jonaschramm/race-tracker/v2-simple/kicad/RaceTracker_v2.kicad_sch

## KiCad design v2-simple/kicad/RaceTracker_v2.kicad_sch (2026-08-14)

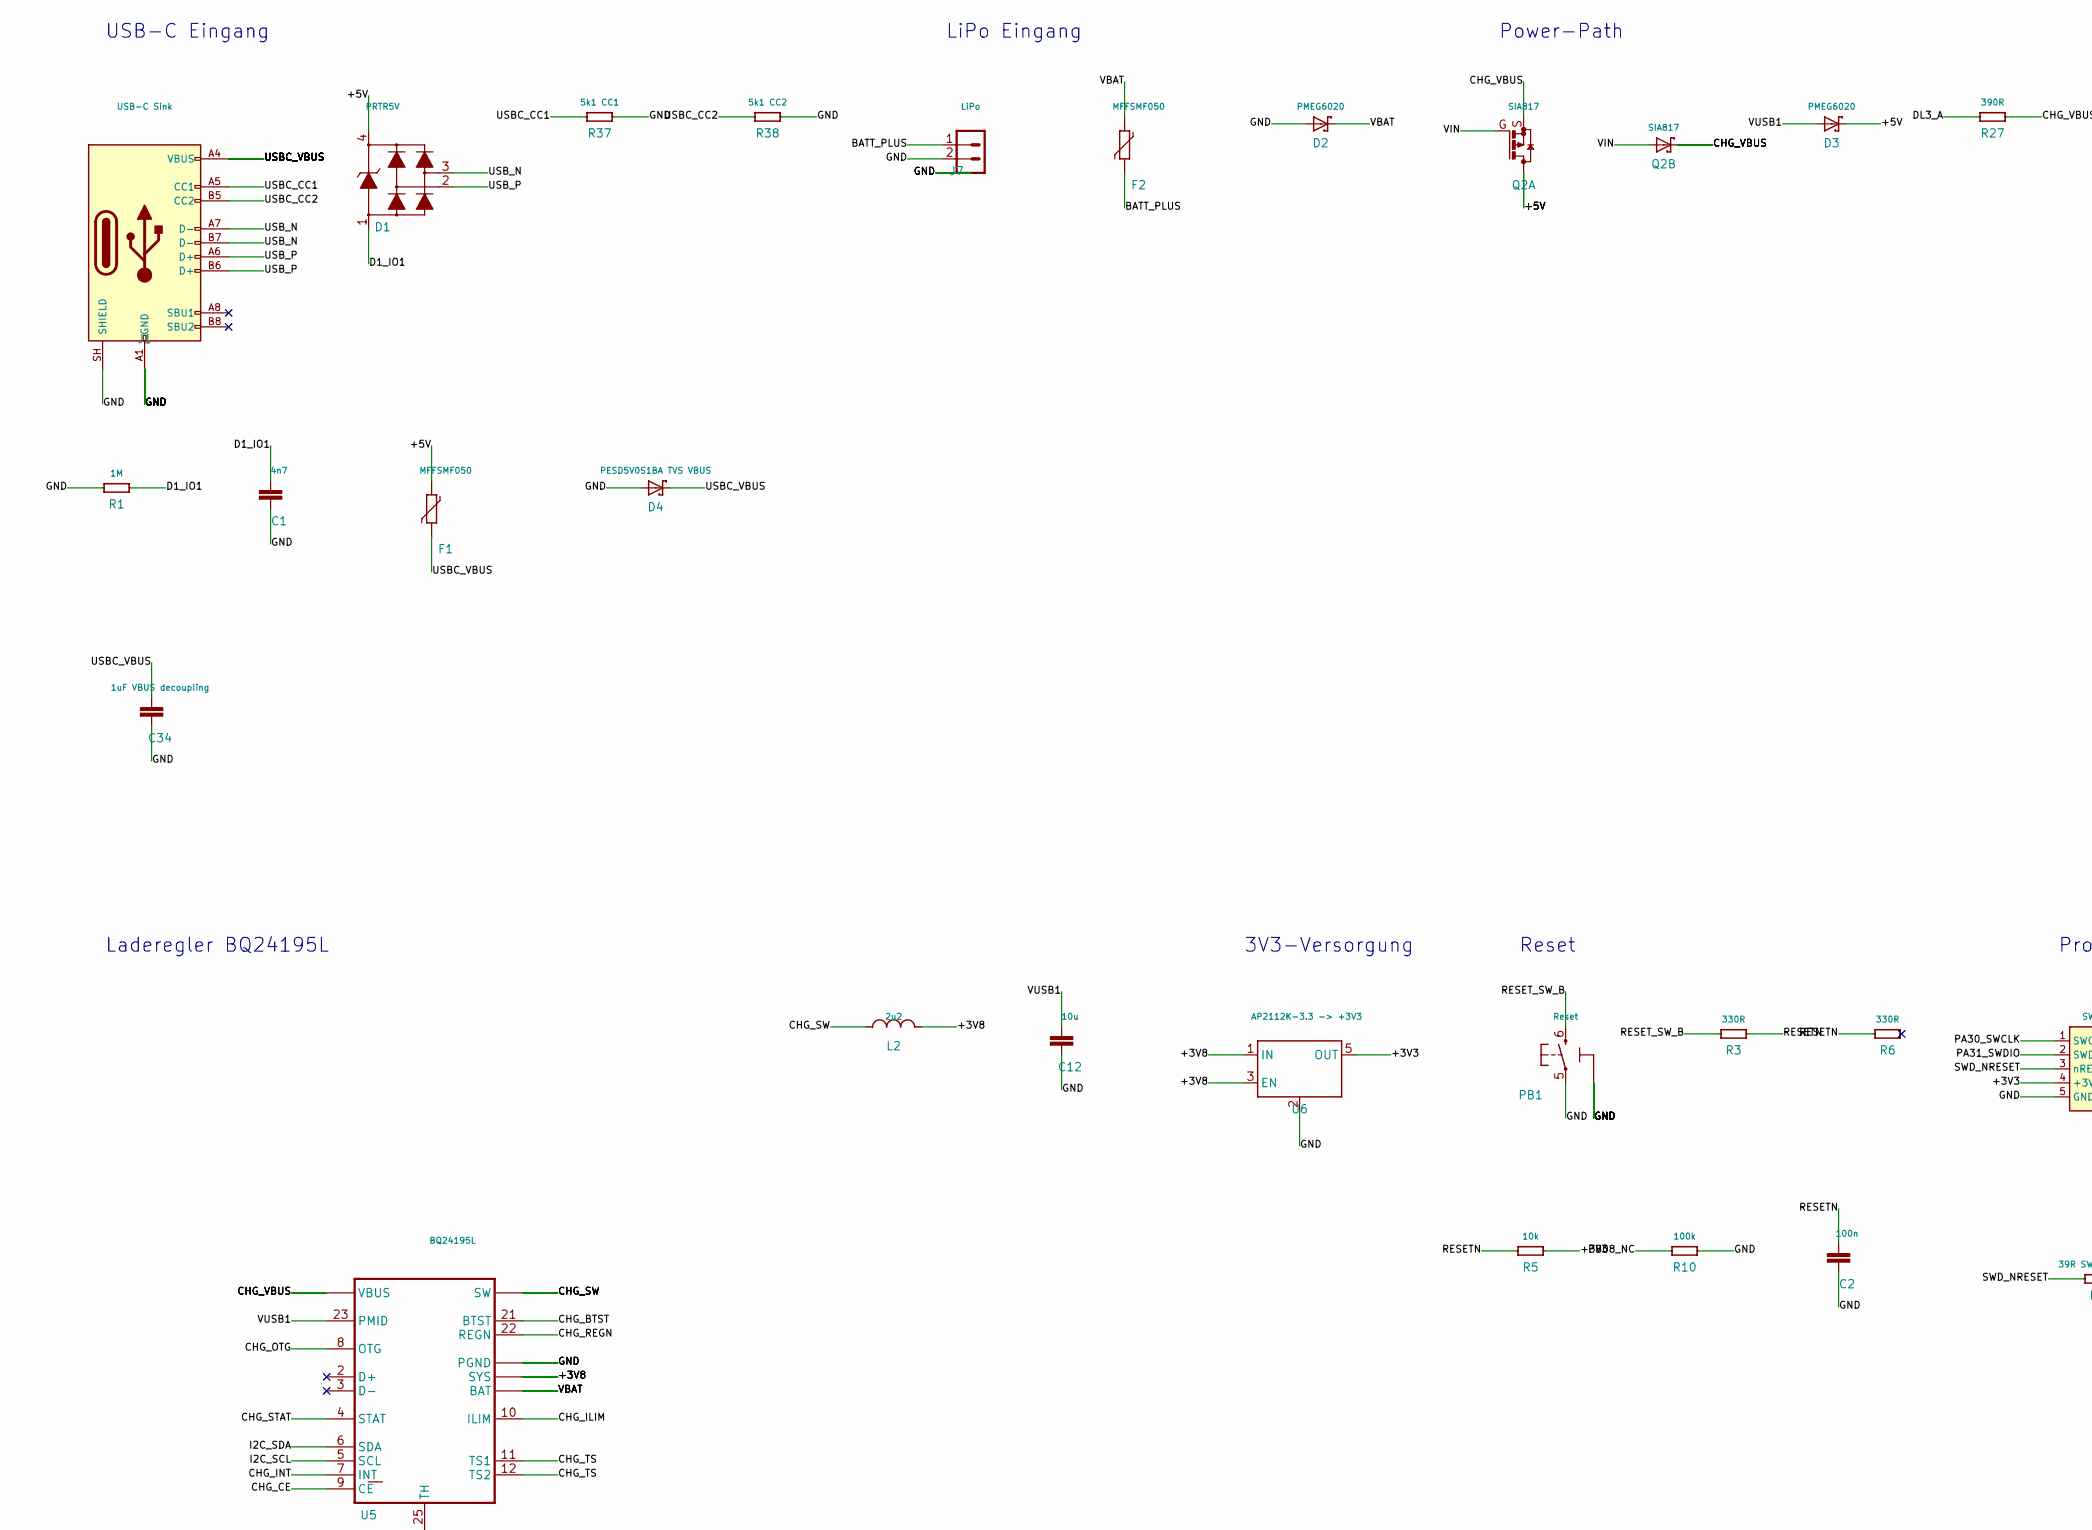
[picture p19: schematic RaceTracker_v2.kicad_sch, part in row 1, column 1]

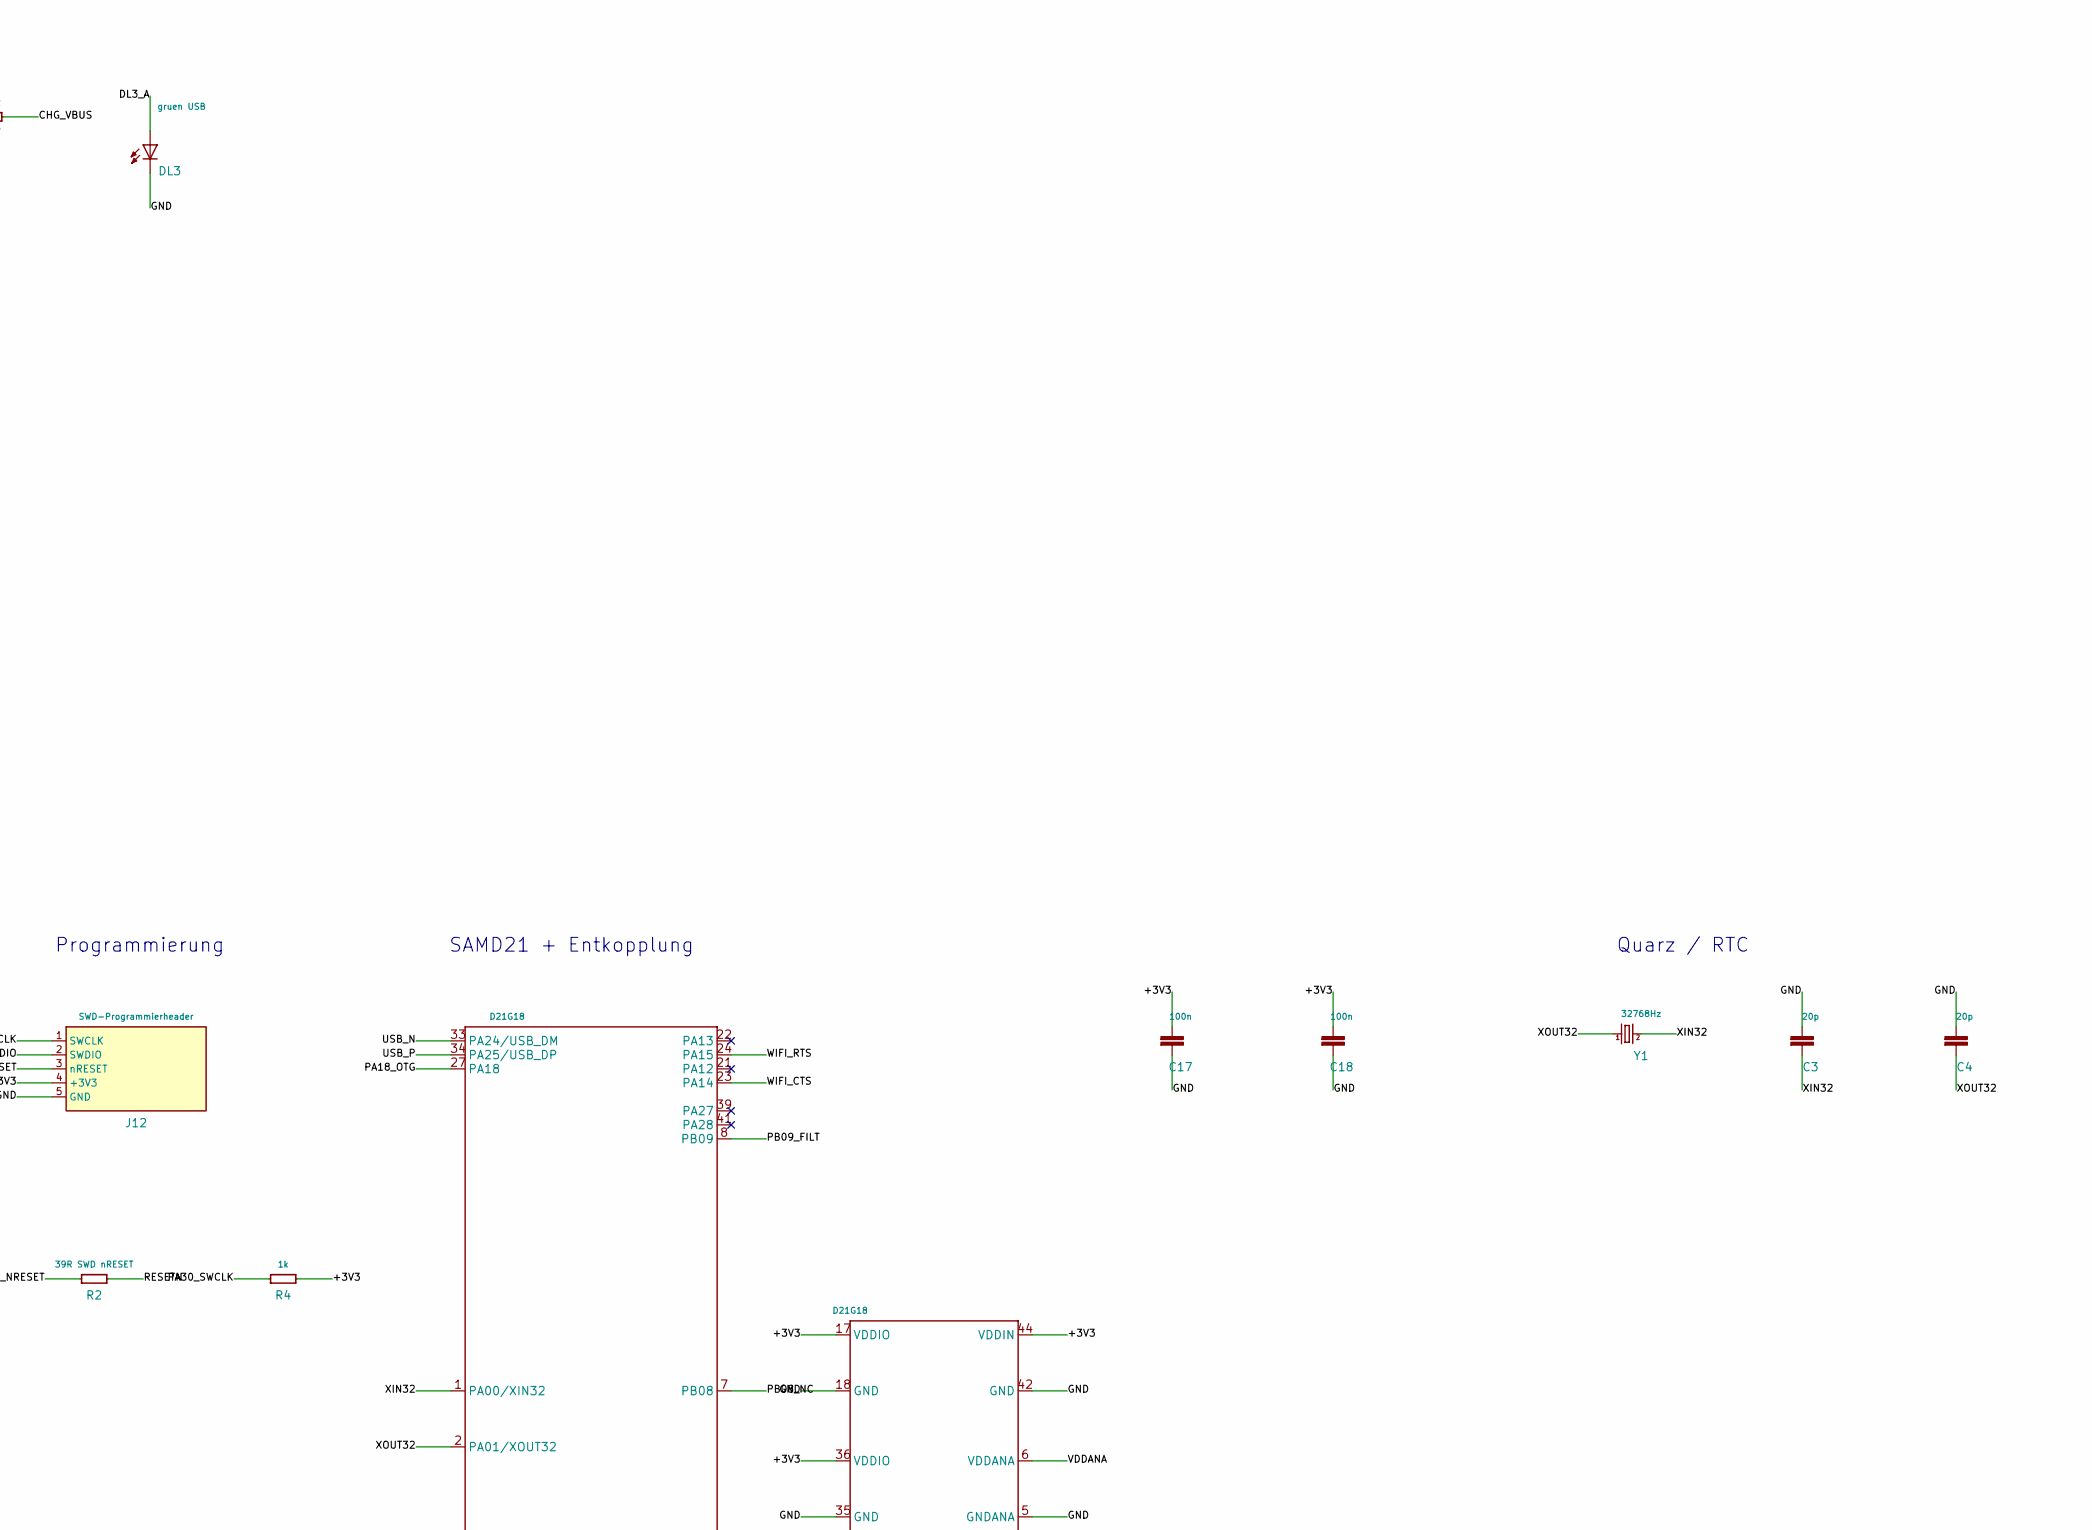
[picture p20: schematic RaceTracker_v2.kicad_sch, part in row 1, column 2]

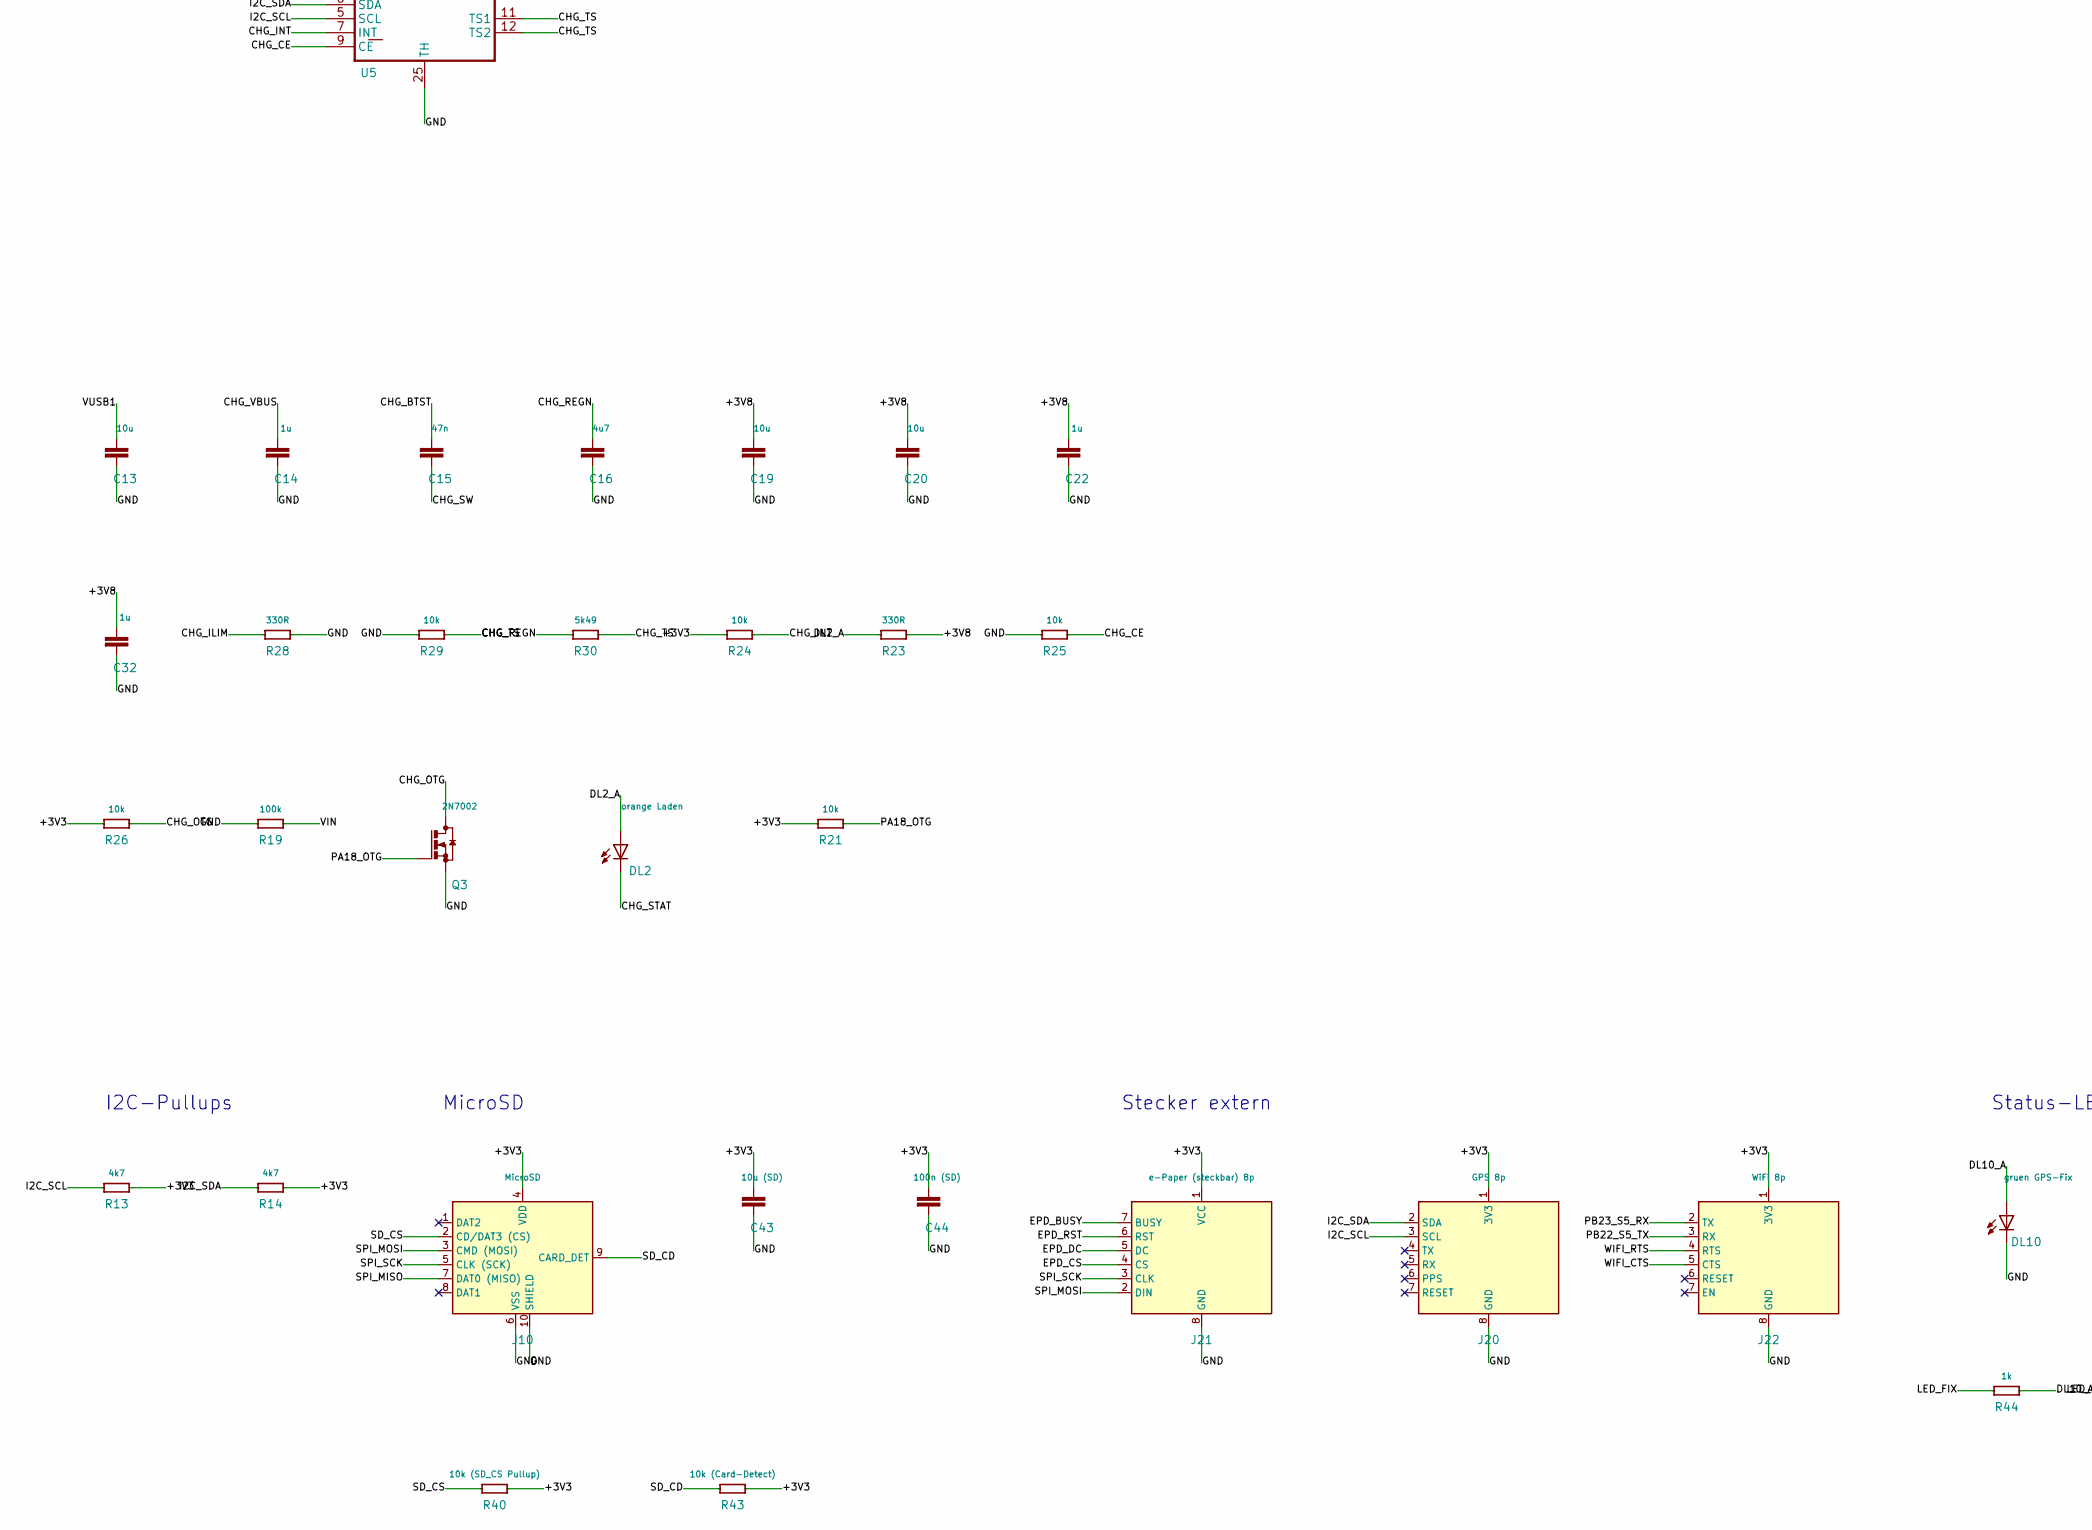
[picture p21: schematic RaceTracker_v2.kicad_sch, part in row 2, column 1]

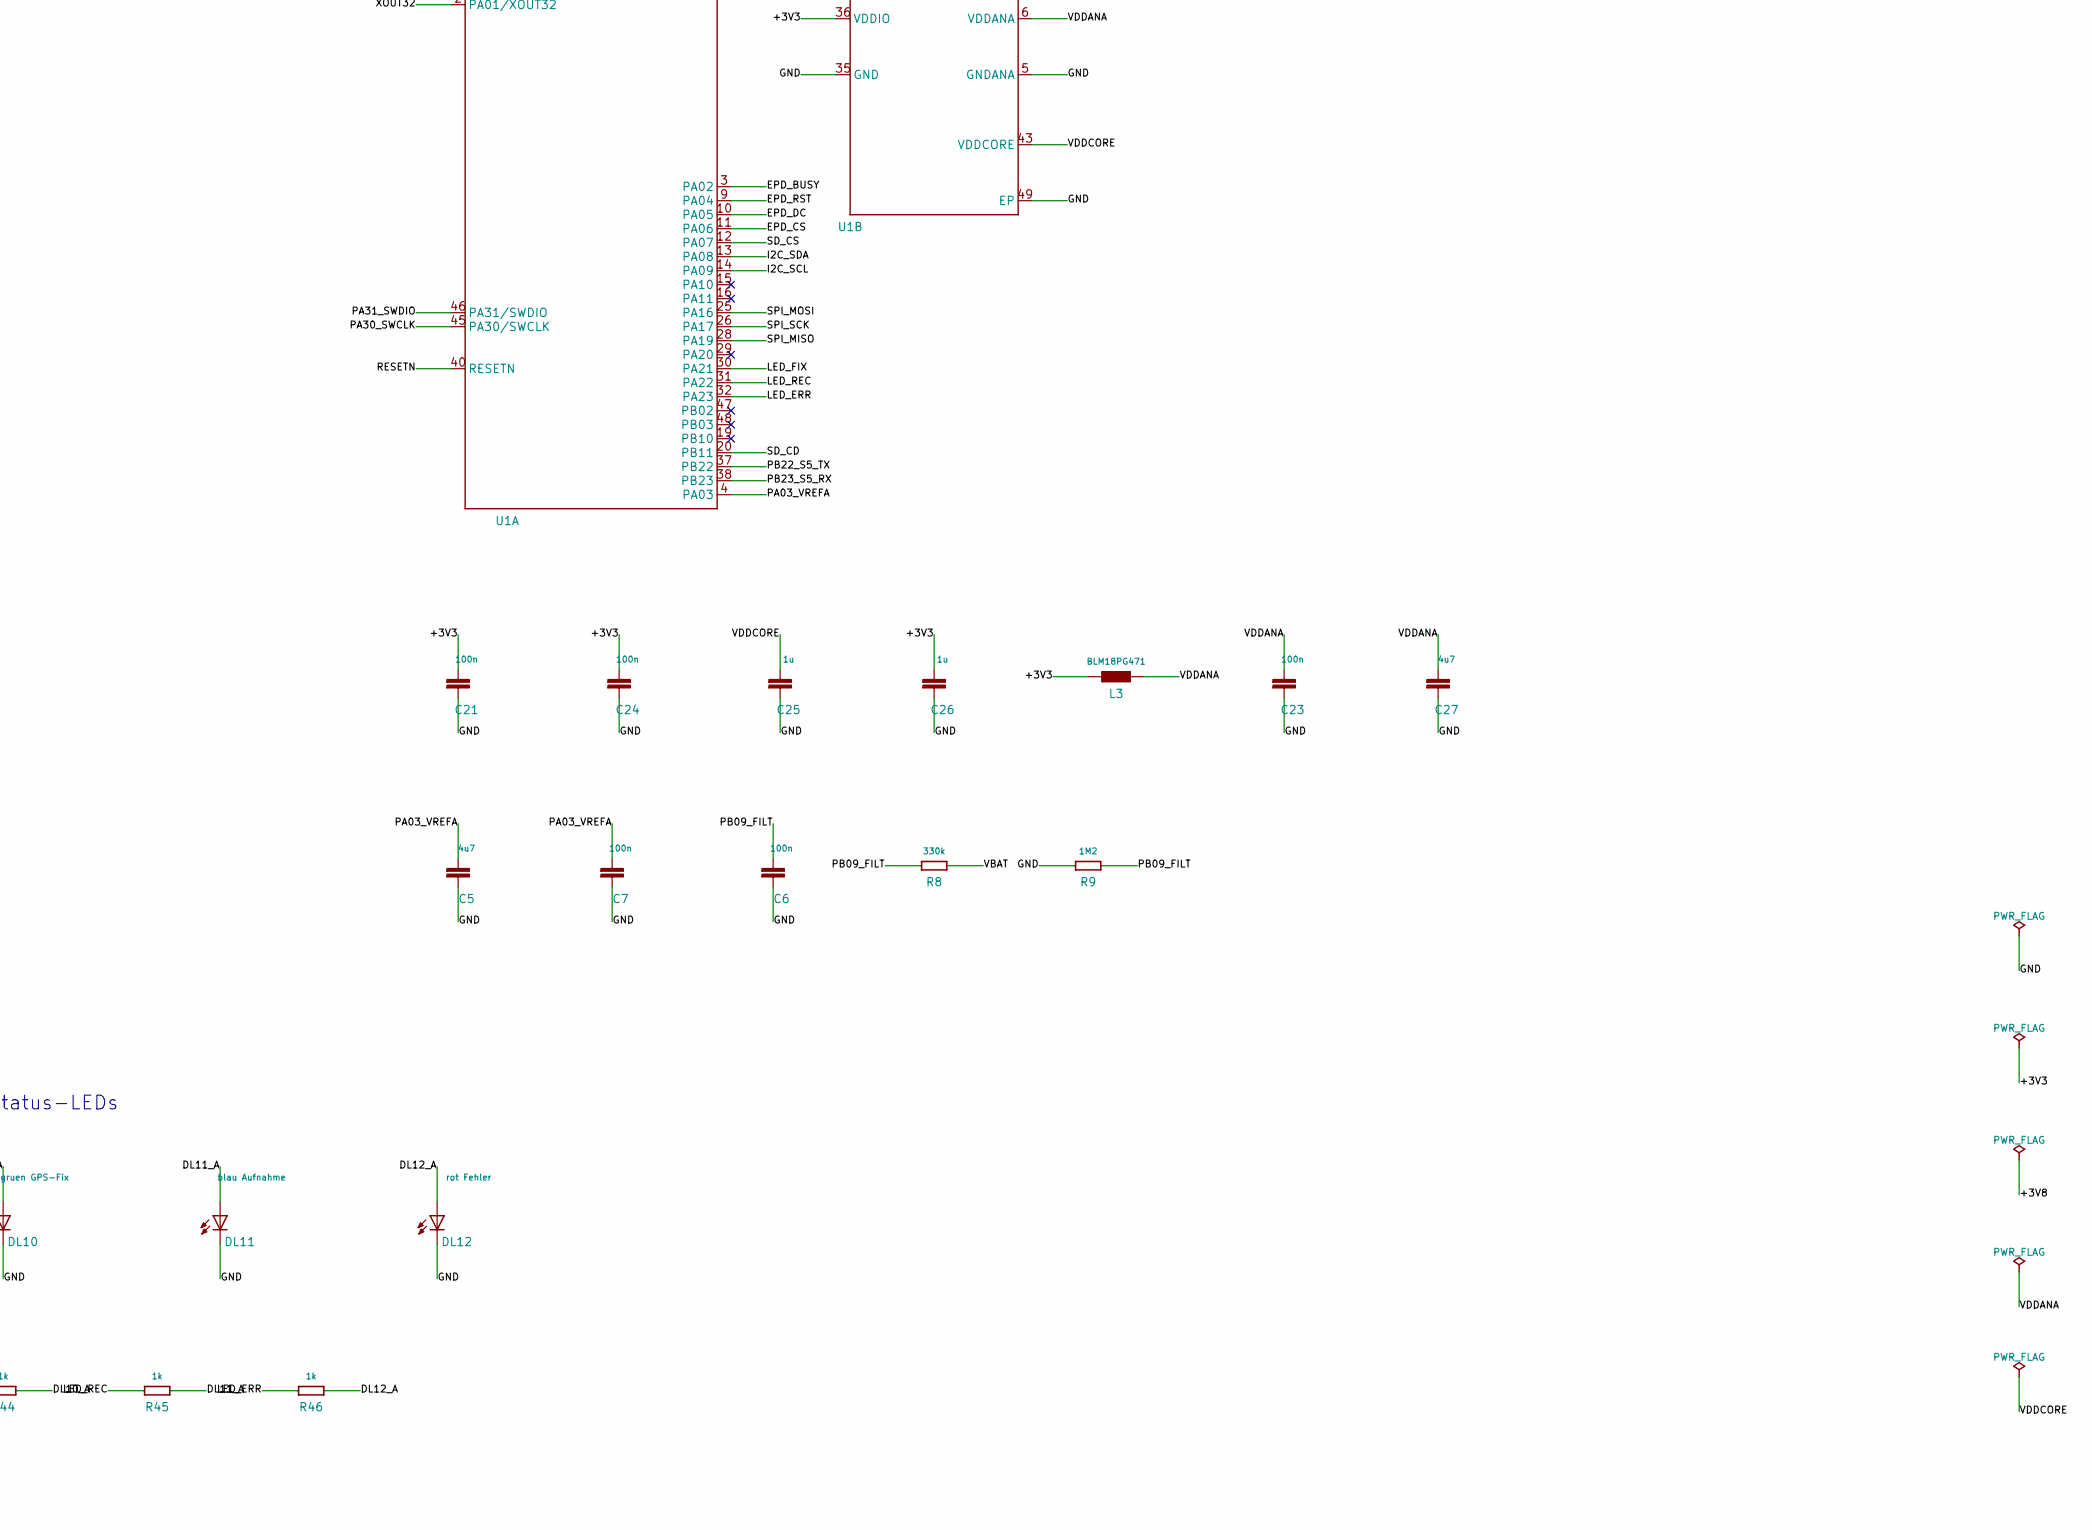
[picture p22: schematic RaceTracker_v2.kicad_sch, part in row 2, column 2]

Parts:
C1: 4n7; C_0805_2012Metric
C2, C6, C7, C17, C18, C21, C23, C24: 100n; C_0402_1005Metric
C3, C4: 20p; C_0402_1005Metric
C5, C16: 4u7; C_0402_1005Metric
C12, C13, C19, C20: 10u; C_0603_1608Metric
C14, C22, C25, C26, C32: 1u; C_0402_1005Metric
C15: 47n; C_0402_1005Metric
C27: 4u7; C_0603_1608Metric
C34: 1uF VBUS decoupling; C_0402_1005Metric
C43: 10u (SD); C_0603_1608Metric
C44: 100n (SD); C_0402_1005Metric
D1: PRTR5V; SOT143B_4N
D2, D3: PMEG6020; SODFL3517X110N
D4: PESD5V0S1BA TVS VBUS; D_SOD-323
DL2: orange Laden; LED_0603_AK
DL3: gruen USB; LED_0603_AK
DL10: gruen GPS-Fix; LED_0603_AK
DL11: blau Aufnahme; LED_0603_AK
DL12: rot Fehler; LED_0603_AK
F1, F2: MFFSMF050; Fuse_0603_1608Metric
J1: USB-C Sink; USB_C_Receptacle_HRO_TYPE-C-31-M-12
J7: LiPo; JST_S2B_PH_SM4_TB
J10: MicroSD; microSD_HC_Molex_104031-0811
J12: SWD-Programmierheader; PinHeader_1x05_P2.54mm_Vertical
J20: GPS 8p; PinHeader_1x08_P2.54mm_Vertical
J21: e-Paper (steckbar) 8p; PinHeader_1x08_P2.54mm_Vertical
J22: WiFi 8p; PinHeader_1x08_P2.54mm_Vertical
L2: 2u2; SRP4020
L3: BLM18PG471; L_0603_1608Metric
PB1: Reset; PTS820_NO_HOLES
Q2: SIA817; SON65P205X205X75-8N-MWSD
Q3: 2N7002; SOTFL50P160X78-3
R1: 1M; R_0402_1005Metric
R2: 39R SWD nRESET; R_0402_1005Metric
R3, R6, R23, R28: 330R; R_0402_1005Metric
R4, R44, R45, R46: 1k; R_0402_1005Metric
R5, R21, R24, R25, R26, R29: 10k; R_0402_1005Metric
R8: 330k; R_0402_1005Metric
R9: 1M2; R_0402_1005Metric
R10, R19: 100k; R_0402_1005Metric
R13, R14: 4k7; R_0402_1005Metric
R27: 390R; R_0402_1005Metric
R30: 5k49; R_0402_1005Metric
R37: 5k1 CC1; R_0402_1005Metric
R38: 5k1 CC2; R_0402_1005Metric
R40: 10k (SD_CS Pullup); R_0402_1005Metric
R43: 10k (Card-Detect); R_0402_1005Metric
U1: D21G18; QFN48_SAMD21G18A
U5: BQ24195L; QFN24_BQ24195L
U6: AP2112K-3.3 -> +3V3; SOT25
Y1: 32768Hz; ABS07_CRYSTAL

Connections:
+3V3: C17.1, C18.1, C21.1, C24.1, C26.1, C43.1, C44.1, J10.4 (VDD), J12.4 (+3V3), J20.1 (3V3), J21.1 (VCC), J22.1 (3V3), L3.1, R4.2, R5.2, R13.2, R14.2, R21.1, R24.1, R26.1, R40.2, R43.2, U1.17 (VDDIO), U1.36 (VDDIO), U1.44 (VDDIN), U6.5 (OUT)
+3V8: C19.1, C20.1, C22.1, C32.1, L2.2, R23.2, U5.15 (SYS), U5.16 (SYS), U6.1 (IN), U6.3 (EN)
+5V: D1.4, D3.C, F1.2, Q2.D, Q2.D2 (D)
BATT_PLUS: F2.1, J7.1
CHG_BTST: C15.1, U5.21 (BTST)
CHG_CE: R25.2, U5.9 (CE)
CHG_ILIM: R28.1, U5.10 (ILIM)
CHG_INT: R24.2, U5.7 (INT)
CHG_OTG: Q3.D, R26.2, U5.8 (OTG)
CHG_REGN: C16.1, R30.1, U5.22 (REGN)
CHG_STAT: DL2.C, U5.4 (STAT)
CHG_SW: C15.2, L2.1, U5.19 (SW), U5.20 (SW)
CHG_TS: R29.2, R30.2, U5.11 (TS1), U5.12 (TS2)
CHG_VBUS: C14.1, Q2.K (C), Q2.K2 (C), Q2.S, R27.2, U5.1 (VBUS), U5.24 (VBUS)
D1_IO1: C1.1, D1.1, R1.2
DL2_A: DL2.A, R23.1
DL3_A: DL3.A, R27.1
DL10_A: DL10.A, R44.2
DL11_A: DL11.A, R45.2
DL12_A: DL12.A, R46.2
EPD_BUSY: J21.7 (BUSY), U1.3 (PA02)
EPD_CS: J21.4 (CS), U1.11 (PA06)
EPD_DC: J21.5 (DC), U1.10 (PA05)
EPD_RST: J21.6 (RST), U1.9 (PA04)
GND: C1.2, C2.2, C3.1, C4.1, C5.2, C6.2, C7.2, C12.2, C13.2, C14.2, C16.2, C17.2, C18.2, C19.2, C20.2, C21.2, C22.2, C23.2, C24.2, C25.2, C26.2, C27.2, C32.2, C34.2, C43.2, C44.2, D2.A, D4.A, DL3.C, DL10.C, DL11.C, DL12.C, J1.A1 (GND), J1.A12 (GND), J1.B1 (GND), J1.B12 (GND), J1.SH (SHIELD), J7.2, J7.3 (SH), J7.4 (SH), J10.6 (VSS), J10.10 (SHIELD), J12.5 (GND), J20.8 (GND), J21.8 (GND), J22.8 (GND), PB1.1 (3), PB1.2 (3), PB1.3, PB1.4 (3), PB1.5 (1), Q3.S, R1.1, R9.1, R10.2, R19.1, R25.1, R28.2, R29.1, R37.2, R38.2, U1.5 (GNDANA), U1.18 (GND), U1.35 (GND), U1.42 (GND), U1.49 (EP), U5.17 (PGND), U5.18 (PGND), U5.25 (TH), U6.2 (GND/ADJ)
I2C_SCL: J20.3 (SCL), R13.1, U1.14 (PA09), U5.5 (SCL)
I2C_SDA: J20.2 (SDA), R14.1, U1.13 (PA08), U5.6 (SDA)
LED_ERR: R46.1, U1.32 (PA23)
LED_FIX: R44.1, U1.30 (PA21)
LED_REC: R45.1, U1.31 (PA22)
PA03_VREFA: C5.1, C7.1, U1.4 (PA03)
PA18_OTG: Q3.G, R21.2, U1.27 (PA18)
PA30_SWCLK: J12.1 (SWCLK), R4.1, U1.45 (PA30/SWCLK)
PA31_SWDIO: J12.2 (SWDIO), U1.46 (PA31/SWDIO)
PB08_NC: R10.1, U1.7 (PB08)
PB09_FILT: C6.1, R8.1, R9.2, U1.8 (PB09)
PB22_S5_TX: J22.3 (RX), U1.37 (PB22)
PB23_S5_RX: J22.2 (TX), U1.38 (PB23)
RESETN: C2.1, R2.2, R3.2, R5.1, R6.1, U1.40 (RESETN)
RESET_SW_B: PB1.6 (2), R3.1
SD_CD: J10.9 (CARD_DET), R43.1, U1.20 (PB11)
SD_CS: J10.2 (CD/DAT3 (CS)), R40.1, U1.12 (PA07)
SPI_MISO: J10.7 (DAT0 (MISO)), U1.28 (PA19)
SPI_MOSI: J10.3 (CMD (MOSI)), J21.2 (DIN), U1.25 (PA16)
SPI_SCK: J10.5 (CLK (SCK)), J21.3 (CLK), U1.26 (PA17)
SWD_NRESET: J12.3 (nRESET), R2.1
USBC_CC1: J1.A5 (CC1), R37.1
USBC_CC2: J1.B5 (CC2), R38.1
USBC_VBUS: C34.1, D4.C, F1.1, J1.A4 (VBUS), J1.A9 (VBUS), J1.B4 (VBUS), J1.B9 (VBUS)
USB_N: D1.3, J1.A7 (D-), J1.B7 (D-), U1.33 (PA24/USB_DM)
USB_P: D1.2, J1.A6 (D+), J1.B6 (D+), U1.34 (PA25/USB_DP)
VBAT: D2.C, F2.2, R8.2, U5.13 (BAT), U5.14 (BAT)
VDDANA: C23.1, C27.1, L3.2, U1.6 (VDDANA)
VDDCORE: C25.1, U1.43 (VDDCORE)
VIN: Q2.A, Q2.G, R19.2
VUSB1: C12.1, C13.1, D3.A, U5.23 (PMID)
WIFI_CTS: J22.5 (CTS), U1.23 (PA14)
WIFI_RTS: J22.4 (RTS), U1.24 (PA15)
XIN32: C3.2, U1.1 (PA00/XIN32), Y1.2
XOUT32: C4.2, U1.2 (PA01/XOUT32), Y1.1

Notes on the sheet:
USB-C Eingang
LiPo Eingang
Power-Path
Laderegler BQ24195L
3V3-Versorgung
SAMD21 + Entkopplung
Quarz / RTC
Reset
I2C-Pullups
Programmierung
MicroSD
Status-LEDs
Stecker extern
