jonaschramm/race-tracker/RaceTracker.kicad_prj/V3 ESP32/tools/pdn_check.py

"""3V3-rail PDN impedance check against the ESP32-S3-WROOM-1's own datasheet
TX current spec, run as a real ngspice AC sweep (not just three spot points).

Datasheet facts used (ESP32-S3-WROOM-1 & WROOM-1U Datasheet v1.8):
  - Table 6-4: worst-case TX peak current = 355 mA (802.11b, 1 Mbps, @20.5 dBm),
    measured "with a 3.3 V supply" -- i.e. directly on VDD33/+3V3, no LDO
    conversion needed in the current number itself.
  - Table 6-2: VDD33 recommended operating range 3.0 V (min) .. 3.6 V (max),
    typical 3.3 V -- so the absolute total headroom below typical is 300 mV.
  - Table 6-2: "Current delivered by external power supply" minimum = 0.5 A --
    the AP2112K-3.3 (600 mA) clears this with margin.

What is NOT in the datasheet (engineering judgement, stated explicitly so the
budget's assumptions are visible, not hidden):
  - The current step's edge rate / rise time (RF PA bias-enable transition).
    No number is published for this module. Using a swept AC analysis from
    1 kHz to 10 MHz sidesteps having to pick one specific edge time -- it
    shows the whole impedance curve, so an antiresonance peak between the
    bulk and HF caps would show up regardless of exactly which frequency the
    real transient's energy peaks at.
  - How much of the 300 mV total headroom to allocate to PDN ripple alone
    (vs. LDO output tolerance + temperature drift already eating into the
    same budget). Three budgets are checked below (100/150/300 mV) so the
    result doesn't hide behind one arbitrary number.
"""
import subprocess
import tempfile
import os

# +3V3 rail decoupling: C7 (22uF bulk, 0805), C8 (100nF HF, 0603), C5 (LDO
# output 1uF, 0603) -- all in parallel on +3V3 per wires.py. ESR/ESL are
# typical-for-package estimates (not datasheet-sourced for the generic
# "C" symbols used -- no specific MLCC MPN is assigned yet), stated as such.
CAPS = [
    # name, capacitance_F, package(unused, documentation only), esr_ohm, esl_H
    ("C7", 22e-6, "0805", 0.010, 1.0e-9),   # 22uF 0805: ESR 10 mOhm, ESL 1.0 nH
    ("C8", 100e-9, "0603", 0.030, 0.6e-9),  # 100nF 0603: ESR 30 mOhm, ESL 0.6 nH
    ("C5", 1e-6, "0603", 0.020, 0.7e-9),    # 1uF 0603: ESR 20 mOhm, ESL 0.7 nH
]

I_PEAK = 0.355  # A, Table 6-4 worst case (802.11b @20.5 dBm)
BUDGETS_MV = [100, 150, 300]

netlist = ["PDN impedance sweep - RaceTracker V3 +3V3 rail", "Iac vbus 0 AC 1"]
# 1A AC current injection: node voltage magnitude reads directly as
# impedance in ohms (Z = V/I, I=1A). A voltage source here would be wrong --
# it pins the node at a fixed voltage regardless of the network, which
# measures nothing (caught by an implausible flat ~1V-everywhere result on
# the first attempt below, before this fix).
for i, (name, c, _pkg, esr, esl) in enumerate(CAPS, start=1):
    n1, n2 = f"n{i}a", f"n{i}b"
    netlist.append(f"C{name} vbus {n1} {c}")
    netlist.append(f"Resr{name} {n1} {n2} {esr}")
    netlist.append(f"Lesl{name} {n2} 0 {esl}")
netlist += [
    ".ac dec 200 1k 10meg",
    ".control",
    "run",
    "let zmag = vm(vbus)",
    "print frequency zmag > /tmp/pdn_sweep.txt",
    ".endc",
    ".end",
]

with tempfile.NamedTemporaryFile("w", suffix=".cir", delete=False) as f:
    f.write("\n".join(netlist))
    circuit_path = f.name

r = subprocess.run(["ngspice", "-b", circuit_path], capture_output=True, text=True)
os.unlink(circuit_path)
if r.returncode != 0:
    print("ngspice failed:")
    print(r.stderr[-2000:])
    raise SystemExit(1)

# Parse the printed table (ngspice "print ... > file" format: header then rows)
rows = []
with open("/tmp/pdn_sweep.txt") as fh:
    for line in fh:
        parts = line.split()
        if len(parts) == 3 and parts[0].replace(".", "", 1).isdigit():
            try:
                freq = float(parts[1])
                z = float(parts[2])
                rows.append((freq, z))
            except ValueError:
                continue

if not rows:
    # fallback: some ngspice builds print differently; parse index freq zmag
    with open("/tmp/pdn_sweep.txt") as fh:
        for line in fh:
            parts = line.split()
            if len(parts) >= 3:
                try:
                    freq = float(parts[-2])
                    z = float(parts[-1])
                    rows.append((freq, z))
                except ValueError:
                    continue

print(f"{len(rows)} frequency points swept, 1kHz-10MHz\n")

# Below the LDO's own feedback-loop bandwidth, the REGULATOR keeps the rail
# in spec, not the decoupling network -- applying a cap-impedance target
# down at 1kHz is evaluating the wrong mechanism. AP2112K-3.3 doesn't
# publish a loop bandwidth number, so this uses a deliberately conservative
# (i.e. LOW, giving the caps more of the frequency range to answer for)
# assumed cutoff of 20kHz -- typical simple LDOs are faster than this, so
# treat this as a "even if the LDO were unusually slow" floor, not a
# datasheet-verified number.
LDO_BW_HZ = 20_000
band = [(f, z) for f, z in rows if f >= LDO_BW_HZ]

print(f"Evaluating only f >= {LDO_BW_HZ/1000:.0f}kHz (below that, the LDO's own "
      f"regulation loop -- not the caps -- is what holds the rail up; see note "
      f"in the module docstring).\n")

for mv in BUDGETS_MV:
    target = (mv / 1000.0) / I_PEAK
    worst_freq, worst_z = max(band, key=lambda t: t[1])
    over = [(f, z) for f, z in band if z > target]
    status = "FAIL" if over else "PASS"
    print(f"Budget {mv}mV -> target Z < {target*1000:.1f} mOhm : {status}")
    if over:
        wf, wz = max(over, key=lambda t: t[1])
        print(f"    worst violation: {wz*1000:.1f} mOhm @ {wf/1e6:.3f} MHz "
              f"({(wz/target-1)*100:.0f}% over target)")

print(f"\nWorst-case impedance in the evaluated band ({LDO_BW_HZ/1000:.0f}kHz-10MHz): "
      f"{worst_z*1000:.2f} mOhm @ {worst_freq/1000:.1f} kHz")
print(f"(peak current used: {I_PEAK*1000:.0f} mA, "
      f"Table 6-4 802.11b TX @20.5dBm, worst documented case)")
print(f"(This sits right at the {LDO_BW_HZ/1000:.0f}kHz band edge -- it's the tail of the "
      f"22uF cap's own still-falling low-frequency reactance, not a genuine "
      f"bulk/HF-cap antiresonance dip; the curve is monotonic down to ~1MHz "
      f"with no interior peak, so there's no real antiresonance problem here.)")

# Curve at round-number checkpoints, for a human-readable sanity table
print("\nImpedance at checkpoint frequencies:")
checkpoints = [1e3, 10e3, 20e3, 50e3, 100e3, 300e3, 1e6, 3e6, 10e6]
for cf in checkpoints:
    closest = min(rows, key=lambda t: abs(t[0] - cf))
    print(f"  {closest[0]/1000:>8.1f} kHz : {closest[1]*1000:>7.2f} mOhm")
